arisfebriyanto193/scales-onemed/desain-web/WhatsApp Image 2026-06-04 at 14.35.00 (1).jpeg

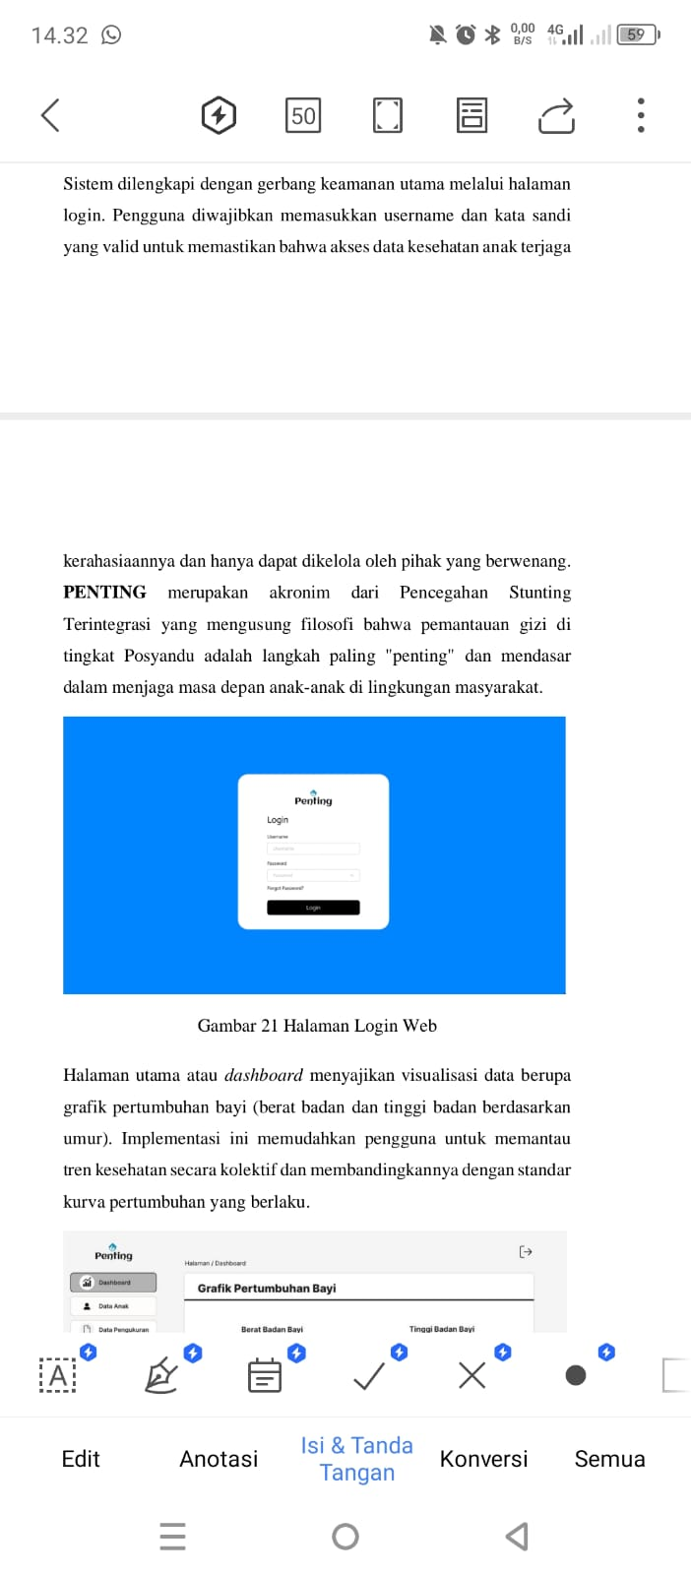
desain-web/WhatsApp Image 2026-06-04 at 14.35.00 (1).jpeg
